ZipCPU/sdr/rtl/fmdemod.v

////////////////////////////////////////////////////////////////////////////////
//
// Filename: 	fmdemod.v
// {{{
// Project:	SDR, a basic Soft(Gate)ware Defined Radio architecture
//
// Purpose:	FM Demodulate an incoming I+Q (1-bit each) signal into the
//		underlying audio data.  The signal processing path includes;
//
//	1. CIC filter, to recover the lost bits from the I+Q sampling.  This
//		also downsamples the signal to a slower rate.
//	2. All but the top bits out of the CIC filter are then discarded
//	3. The result is then fed into an I+Q PLL, to track the frequency
//		of the incoming waveform
//	4. The PLL doesn't output frequency, however, it outputs phase.  The
//		difference between two phases is proportional to frequency,
//		so this difference is placed into a final resampler.
//	5. A gain is applied to the final (audio quality, hopefully) signal, and
//	6. Sent to a PWM audio output device.
//
// Creator:	Dan Gisselquist, Ph.D.
//		Gisselquist Technology, LLC
//
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
// This program is distributed in the hope that it will be useful, but WITHOUT
// ANY WARRANTY; without even the implied warranty of MERCHANTIBILITY or
// FITNESS FOR A PARTICULAR PURPOSE.  See the GNU General Public License
// for more details.
//
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
////////////////////////////////////////////////////////////////////////////////
//
//
`default_nettype	none
// }}}
module	fmdemod #(
		// {{{
		// parameter [31:0]	CLOCK_FREQUENCY_HZ = 36_000_000,
		// parameter [31:0]	RAW_DATA_RATE_HZ = 960_000,
		// parameter [31:0]	AUDIO_SAMPLE_RATE_HZ = 48_000,
		parameter		NUM_AUDIO_COEFFS = 666,
		parameter		HIST_BITS = 10,
		localparam	CIC_BITS = 7,
		localparam	BB_BITS  = 16,
		localparam	PWM_BITS = 16,
		localparam	PLL_BITS = 28,
		localparam [PLL_BITS-1:0]	DEFAULT_PLL_STEP = 0,
		//
		// localparam [31:0]	RAW_AUDIO_DOWNSAMPLE_RATIO
		//	= CLOCK_FREQUENCY_HZ / AUDIO_SAMPLE_RATE_HZ, // == 750
		// localparam [31:0]	RAW_AUDIO_DOWNSAMPLE_RATIO = 750,
		localparam		CIC_DOWN = 25,	// About 200kHz B/W
		// localparam		CIC_DOWN = 5,
		localparam [31:0]	SECONDARY_DOWNSAMPLE_RATIO
						= 750 / CIC_DOWN
		// }}}
	) (
		// {{{
		input	wire		i_clk, i_reset,
		input	wire		i_audio_en, i_rf_en,
		//
		// Wishbone interface
		// {{{
		input	wire		i_wb_cyc, i_wb_stb, i_wb_we,
		input	wire [1:0]	i_wb_addr,
		input	wire [31:0]	i_wb_data,
		input	wire	[3:0]	i_wb_sel,
		output	reg		o_wb_stall,
		output	reg		o_wb_ack,
		output	reg	[31:0]	o_wb_data,
		// }}}
		// Receive interface
		input	wire	[1:0]	i_rf_data,
		//
		// Outgoing PWM interface
		output	reg		o_pwm_audio,
		//
		// Debug interface
		// {{{
		input	wire	[1:0]	i_dbg_sel,
		output	reg		o_dbg_ce,
		output	reg	[31:0]	o_dbg_data,
		output reg [HIST_BITS-1:0] o_dbg_hist
		// }}}
		// }}}
	);

	// Signal declarations
	// {{{
	integer	k;

	wire			cic_ce, cic_ign, baseband_ce;
	wire	[CIC_BITS-1:0]	cic_sample_i, cic_sample_q;
	wire signed [BB_BITS-1:0] baseband_sample;
	reg	[PWM_BITS-1:0]	pwm_counter, brev_counter;
	reg signed [31:0]	amplified_sample;
	reg	[15:0]		audio_sample_off;
	// wire			splr_busy, splr_done;
	wire	[PLL_BITS-1:0]	pll_phase;
	reg	[PLL_BITS-1:0]	last_pll_phase, fm_step;
	reg	[4:0]		pll_lgcoeff;
	reg signed [15:0]	r_gain;
	reg			load_pll;
	reg	[PLL_BITS-2:0]	new_pll_step;
	reg			write_audio_filter, reset_filter;
	reg	[15:0]		write_coeff;
	wire	[1:0]		pll_err;
	wire			pll_locked;
	// }}}
	////////////////////////////////////////////////////////////////////////
	//
	// Incoming Bus processing
	// {{{
	////////////////////////////////////////////////////////////////////////
	//
	//
	initial	pll_lgcoeff  = 5'h05;
	initial	new_pll_step = DEFAULT_PLL_STEP[PLL_BITS-2:0];
	initial	load_pll     = 1;
	initial	reset_filter = 1;
	initial	write_audio_filter = 0;
	always @(posedge i_clk)
	if (i_wb_stb && i_wb_we)
	begin
		{ reset_filter, load_pll, write_coeff } <= 0;

		case(i_wb_addr)
		2'b00: r_gain <= i_wb_data[15:0];
		2'b01: { load_pll, new_pll_step } <= { 1'b1,  i_wb_data[PLL_BITS-2:0] };
		2'b10: { reset_filter, write_audio_filter, write_coeff }
				<= { i_wb_data[31], !i_wb_data[31],
						i_wb_data[15:0] };
		2'b11: pll_lgcoeff <= i_wb_data[4:0];
		default: begin end
		endcase
	end else
		{ reset_filter, load_pll, write_coeff } <= 0;

	always @(*)
		o_wb_stall = 1'b0;

	always @(posedge i_clk)
		o_wb_ack <= !i_reset && i_wb_stb;
	//  }}}
	////////////////////////////////////////////////////////////////////////
	//
	// CIC Filters
	// {{{
	////////////////////////////////////////////////////////////////////////
	//
	//
`ifdef	ALT_INCOMING_CIC
	reg	[7+2-1:0]	cic_acci	[0:7];
	reg	[7+2-1:0]	cic_accq	[0:7];
	reg	[7+2-1:0]	last_cic_acci	[0:6];
	reg	[7+2-1:0]	last_cic_accq	[0:6];
	reg	[1:0]		last_rf_data;

	always @(posedge i_clk)
	begin
		cic_acci[0] <= (i_rf_data[1] ? 9'h1ff : 9'h01)
				+ (last_rf_data[1] ? 9'h1ff : 9'h01);
		cic_accq[0] <= (i_rf_data[0] ? 9'h1ff : 9'h01)
				+ (last_rf_data[0] ? 9'h1ff : 9'h01);
		last_rf_data <= i_rf_data;
		{ last_cic_acci[0], last_cic_accq[0] }
				<= { cic_acci[0], cic_accq[0] };

		cic_acci[1] <= cic_acci[0] + last_cic_acci[0];
		cic_accq[1] <= cic_accq[0] + last_cic_accq[0];
		{ last_cic_acci[1], last_cic_accq[1] }
				<= { cic_acci[1], cic_accq[1] };

		cic_acci[2] <= cic_acci[1] + last_cic_acci[1];
		cic_accq[2] <= cic_accq[1] + last_cic_accq[1];
		{ last_cic_acci[2], last_cic_accq[2] }
				<= { cic_acci[2], cic_accq[2] };

		cic_acci[3] <= cic_acci[2] + last_cic_acci[2];
		cic_accq[3] <= cic_accq[2] + last_cic_accq[2];
		{ last_cic_acci[3], last_cic_accq[3] }
			<= { cic_acci[3], cic_accq[3] };

		cic_acci[4] <= cic_acci[3] + last_cic_acci[3];
		cic_accq[4] <= cic_accq[3] + last_cic_accq[3];
		{ last_cic_acci[4], last_cic_accq[4] }
			<= { cic_acci[4], cic_accq[4] };

		cic_acci[5] <= cic_acci[4] + last_cic_acci[4];
		cic_accq[5] <= cic_accq[4] + last_cic_accq[4];
		{ last_cic_acci[5], last_cic_accq[5] }
			<= { cic_acci[5], cic_accq[5] };

		cic_acci[6] <= cic_acci[5] + last_cic_acci[5];
		cic_accq[6] <= cic_accq[5] + last_cic_accq[5];
		{ last_cic_acci[6], last_cic_accq[6] }
			<= { cic_acci[6], cic_accq[6] };

		cic_acci[7] <= cic_acci[3] + last_cic_acci[6];
		cic_accq[7] <= cic_accq[3] + last_cic_accq[6];
		// { last_cic_acci[7], last_cic_accq[7] }
		//	<= { cic_acci[7], cic_accq[7] };
	end

	assign	cic_ce = 1'b1;

	assign	cic_sample_i = cic_acci[7][8:3] - 7'h10;
	assign	cic_sample_q = cic_accq[7][8:3]- 7'h10;
	assign	cic_ign = 1'b0;
`else

	cicfil #(.IW(2), .OW(CIC_BITS), .STAGES(4), .LGMEM(28), .SHIFT(10))
	cici(i_clk, reset_filter, CIC_DOWN[6:0], 1'b1, i_rf_data[1] ? 2'b01 : 2'b11, cic_ce, cic_sample_i);

	cicfil #(.IW(2), .OW(CIC_BITS), .STAGES(4), .LGMEM(28), .SHIFT(10))
	cicq(i_clk, reset_filter, CIC_DOWN[6:0], 1'b1, i_rf_data[0] ? 2'b01 : 2'b11, cic_ign, cic_sample_q);

`endif	// ALT_INCOMING_CIC
	// }}}
	////////////////////////////////////////////////////////////////////////
	//
	// Track the FM carrier
	// {{{
	////////////////////////////////////////////////////////////////////////
	//
	//

	quadpll #(.PHASE_BITS(PLL_BITS), .OPT_TRACK_FREQUENCY(1'b1),
		.INITIAL_PHASE_STEP(DEFAULT_PLL_STEP))// i.e. TRACKING FREQUENCY
	carrier_track(i_clk, load_pll, new_pll_step,
		cic_ce, { cic_sample_i[CIC_BITS-1], cic_sample_q[CIC_BITS-1] },
			pll_lgcoeff, pll_phase, pll_err, pll_locked);

	always @(posedge i_clk)
	if (cic_ce)
	begin
		fm_step <= pll_phase - last_pll_phase;
		last_pll_phase <= pll_phase;
	end

`ifdef	CIC_STEP
	reg	[PLL_BITS+7-1:0]	cic_step	[0:7];
	reg	[PLL_BITS+7-1:0]	last_step	[0:6];
	reg	[PLL_BITS+7-1:0]	last_fm_step;
	reg				step_ce;
	reg	[4:0]			step_counter;

	always @(posedge i_clk)
	if (cic_ce)
	begin
		cic_step[0] <= { {(7){fm_step[23]}}, fm_step } + last_fm_step;
		cic_step[1] <= cic_step[0] + last_step[0];
		cic_step[2] <= cic_step[1] + last_step[1];
		cic_step[3] <= cic_step[2] + last_step[2];
		cic_step[4] <= cic_step[3] + last_step[3];
		cic_step[5] <= cic_step[4] + last_step[4];
		cic_step[6] <= cic_step[5] + last_step[5];
		cic_step[7] <= cic_step[6] + last_step[6];

		last_fm_step <= { {(7){fm_step[23]}}, fm_step };
		last_step[0] <= cic_step[0];
		last_step[1] <= cic_step[1];
		last_step[2] <= cic_step[2];
		last_step[3] <= cic_step[3];
		last_step[4] <= cic_step[4];
		last_step[5] <= cic_step[5];
		last_step[6] <= cic_step[6];

		step_ce <= 0;
		step_counter <= step_counter - 1;
		if (step_counter == 0)
		begin
			step_ce <= 1;
			step_counter <= CIC_DOWN[4:0]-1;
		end
	end else
		step_ce <= 0;
`endif
	// }}}
	////////////////////////////////////////////////////////////////////////
	//
	// Downsampling (PLL cleanup)
	// {{{
	////////////////////////////////////////////////////////////////////////
	//
	//

	subfildown #(.IW(BB_BITS), .OW(BB_BITS), .CW(12),
		.INITIAL_COEFFS("amdemod.hex"),
		.SHIFT(10),
		.NDOWN(SECONDARY_DOWNSAMPLE_RATIO),
		.FIXED_COEFFS(1'b0), .NCOEFFS(NUM_AUDIO_COEFFS))
	resample(i_clk, reset_filter,
		write_audio_filter, write_coeff[15:4],
		// cic_ce, cic_step[7][PLL_BITS+7-3-1:PLL_BITS+7-3-BB_BITS],
		cic_ce, fm_step[PLL_BITS-1:PLL_BITS-BB_BITS],
		baseband_ce, baseband_sample);
	// }}}
	////////////////////////////////////////////////////////////////////////
	//
	// Amplify the result
	// {{{
	////////////////////////////////////////////////////////////////////////
	//
	//

	(* mul2dsp *)
	always @(posedge  i_clk)
	// if (splr_done)
		amplified_sample <= baseband_sample[15:0] * r_gain;
	// }}}
	////////////////////////////////////////////////////////////////////////
	//
	// Convert to PWM
	// {{{
	////////////////////////////////////////////////////////////////////////
	//
	//

	always @(posedge  i_clk)
	// if (splr_done)
	begin
		audio_sample_off[14:0] <=  amplified_sample[30:16];
		audio_sample_off[15]   <= !amplified_sample[31];
	end

	always @(posedge i_clk)
		pwm_counter <= pwm_counter + 1;

	always @(*)
	for(k=0; k<PWM_BITS; k=k+1)
		brev_counter[k] = pwm_counter[PWM_BITS-1-k];

	always @(posedge i_clk)
	if (!i_audio_en)
		o_pwm_audio <= !o_pwm_audio;
	else
		o_pwm_audio <= (brev_counter < audio_sample_off);

	// }}}
	////////////////////////////////////////////////////////////////////////
	//
	// Create the debugging outputs
	// {{{
	////////////////////////////////////////////////////////////////////////
	//
	//

	always @(posedge i_clk)
	case(i_dbg_sel)
	2'b00: { o_dbg_ce, o_dbg_data, o_dbg_hist } <= { cic_ce,
			{(16-CIC_BITS){cic_sample_i[CIC_BITS-1]}}, cic_sample_i,
			{(16-CIC_BITS){cic_sample_q[CIC_BITS-1]}}, cic_sample_q,
			cic_sample_i[CIC_BITS-1:CIC_BITS-(HIST_BITS/2)],
			cic_sample_q[CIC_BITS-1:CIC_BITS-(HIST_BITS/2)] };
	2'b10: { o_dbg_ce, o_dbg_data, o_dbg_hist } <= { cic_ce,
				{(32-PLL_BITS){1'b0}}, fm_step,
				fm_step[PLL_BITS-1:PLL_BITS-HIST_BITS] };
	2'b01: { o_dbg_ce, o_dbg_data, o_dbg_hist } <= { baseband_ce,
				{(32-BB_BITS){1'b0}}, baseband_sample,
				baseband_sample[BB_BITS-1:BB_BITS-HIST_BITS] };
	2'b11: { o_dbg_ce, o_dbg_data, o_dbg_hist }
			<= { baseband_ce, amplified_sample,
			amplified_sample[32-1:32-HIST_BITS] };
	default: { o_dbg_ce, o_dbg_data, o_dbg_hist } <= 0;
	endcase

	always @(*)
		o_wb_data = o_dbg_data;
	// }}}

	// Make Verilator happy
	// {{{
	// Verilator lint_off UNUSED
	wire	unused;
	assign	unused = &{ 1'b0, i_wb_cyc, i_wb_sel,
			cic_ign,
			i_rf_en, write_coeff[3:0], pll_err, i_wb_data[30:23],
			amplified_sample[15:0], fm_step[23:16],
			write_audio_filter, write_coeff, pll_locked };
	// Verilator lint_on  UNUSED
	// }}}
endmodule
