ZipCPU/sdr/rtl/seqcordic.v

////////////////////////////////////////////////////////////////////////////////
//
// Filename: 	seqcordic.v
// {{{
// Project:	SDR, a basic Soft(Gate)ware Defined Radio architecture
//
// Purpose:	This file executes a vector rotation on the values
//		(i_xval, i_yval).  This vector is rotated left by
//	i_phase.  i_phase is given by the angle, in radians, multiplied by
//	2^32/(2pi).  In that fashion, a two pi value is zero just as a zero
//	angle is zero.
//
//	This particular version of the CORDIC processes one value at a
//	time in a sequential, vs pipelined or parallel, fashion.
//
// Creator:	Dan Gisselquist, Ph.D.
//		Gisselquist Technology, LLC
//
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
// This program is distributed in the hope that it will be useful, but WITHOUT
// ANY WARRANTY; without even the implied warranty of MERCHANTIBILITY or
// FITNESS FOR A PARTICULAR PURPOSE.  See the GNU General Public License
// for more details.
//
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
//
////////////////////////////////////////////////////////////////////////////////
//
//
`default_nettype	none
// }}}
module	seqcordic #(
		// {{{
		// These parameters are fixed by the core generator.  They
		// have been used in the definitions of internal constants,
		// so they can't really be changed here.
		localparam	IW= 8,	// The number of bits in our inputs
				OW= 8,	// The number of output bits to produce
				// NSTAGES=11,
				// XTRA= 3,// Extra bits for internal precision
				WW=11,	// Our working bit-width
				PW=16	// Bits in our phase variables
		// }}}
	) (
		// {{{
		input	wire				i_clk, i_reset, i_stb,
		input	wire	signed	[(IW-1):0]	i_xval, i_yval,
		input	wire		[(PW-1):0]	i_phase,
		output	wire				o_busy,
		output	reg				o_done,
		output	reg	signed	[(OW-1):0]	o_xval, o_yval
		// }}}
	);
	// First step: expand our input to our working width.
	// {{{
	// This is going to involve extending our input by one
	// (or more) bits in addition to adding any xtra bits on
	// bits on the right.  The one bit extra on the left is to
	// allow for any accumulation due to the cordic gain
	// within the algorithm.
	// 
	wire	signed [(WW-1):0]	e_xval, e_yval;
	assign	e_xval = { {i_xval[(IW-1)]}, i_xval, {(WW-IW-1){1'b0}} };
	assign	e_yval = { {i_yval[(IW-1)]}, i_yval, {(WW-IW-1){1'b0}} };

	// }}}
	// Declare variables for all of the separate stages
	// {{{
	reg	signed	[(WW-1):0]	xv, prex, yv, prey;
	reg		[(PW-1):0]	ph, preph;
	reg				idle, pre_valid;
	reg		[3:0]		state;

	// First step, get rid of all but the last 45 degrees
	// {{{
	// The resulting phase needs to be between -45 and 45
	// degrees but in units of normalized phase
	//
	// We'll do this by walking through all possible quick phase
	// shifts necessary to constrain the input to within +/- 45
	// degrees.
	always @(posedge i_clk)
	case(i_phase[(PW-1):(PW-3)])
	3'b000: begin	// 0 .. 45, No change
		// {{{
		prex  <=  e_xval;
		prey  <=  e_yval;
		preph <= i_phase;
		end
		// }}}
	3'b001: begin	// 45 .. 90
		// {{{
		prex  <= -e_yval;
		prey  <=  e_xval;
		preph <= i_phase - 16'h4000;
		end
		// }}}
	3'b010: begin	// 90 .. 135
		// {{{
		prex  <= -e_yval;
		prey  <=  e_xval;
		preph <= i_phase - 16'h4000;
		end
		// }}}
	3'b011: begin	// 135 .. 180
		// {{{
		prex  <= -e_xval;
		prey  <= -e_yval;
		preph <= i_phase - 16'h8000;
		end
		// }}}
	3'b100: begin	// 180 .. 225
		// {{{
		prex  <= -e_xval;
		prey  <= -e_yval;
		preph <= i_phase - 16'h8000;
		end
		// }}}
	3'b101: begin	// 225 .. 270
		// {{{
		prex  <=  e_yval;
		prey  <= -e_xval;
		preph <= i_phase - 16'hc000;
		end
		// }}}
	3'b110: begin	// 270 .. 315
		// {{{
		prex  <=  e_yval;
		prey  <= -e_xval;
		preph <= i_phase - 16'hc000;
		end
		// }}}
	3'b111: begin	// 315 .. 360, No change
		// {{{
		prex  <=  e_xval;
		prey  <=  e_yval;
		preph <= i_phase;
		end
		// }}}
	endcase
	// }}}

	// Cordic angle table
	// {{{
	// In many ways, the key to this whole algorithm lies in the angles
	// necessary to do this.  These angles are also our basic reason for
	// building this CORDIC in C++: Verilog just can't parameterize this
	// much.  Further, these angle's risk becoming unsupportable magic
	// numbers, hence we define these and set them in C++, based upon
	// the needs of our problem, specifically the number of stages and
	// the number of bits required in our phase accumulator
	//
	reg	[15:0]	cordic_angle [0:15];
	reg	[15:0]	cangle;

	initial	cordic_angle[ 0] = 16'h12e4; //  26.565051 deg
	initial	cordic_angle[ 1] = 16'h09fb; //  14.036243 deg
	initial	cordic_angle[ 2] = 16'h0511; //   7.125016 deg
	initial	cordic_angle[ 3] = 16'h028b; //   3.576334 deg
	initial	cordic_angle[ 4] = 16'h0145; //   1.789911 deg
	initial	cordic_angle[ 5] = 16'h00a2; //   0.895174 deg
	initial	cordic_angle[ 6] = 16'h0051; //   0.447614 deg
	initial	cordic_angle[ 7] = 16'h0028; //   0.223811 deg
	initial	cordic_angle[ 8] = 16'h0014; //   0.111906 deg
	initial	cordic_angle[ 9] = 16'h000a; //   0.055953 deg
	initial	cordic_angle[10] = 16'h0005; //   0.027976 deg
	initial	cordic_angle[11] = 16'h0002; //   0.013988 deg
	initial	cordic_angle[12] = 16'h0001; //   0.006994 deg
	initial	cordic_angle[13] = 16'h0000; //   0.003497 deg
	initial	cordic_angle[14] = 16'h0000; //   0.001749 deg
	initial	cordic_angle[15] = 16'h0000; //   0.000874 deg
	// {{{
	// Std-Dev    : 0.00 (Units)
	// Phase Quantization: 0.000183 (Radians)
	// Gain is 1.164435
	// You can annihilate this gain by multiplying by 32'hdbd95b16
	// and right shifting by 32 bits.
	// }}}
	// }}}

	// idle
	// {{{
	initial	idle = 1'b1;
	always @(posedge i_clk)
	if (i_reset)
		idle <= 1'b1;
	else if (i_stb)
		idle <= 1'b0;
	else if (state == 10)
		idle <= 1'b1;
	// }}}

	// pre_valid
	// {{{
	initial	pre_valid = 1'b0;
	always @(posedge i_clk)
	if (i_reset)
		pre_valid <= 1'b0;
	else
		pre_valid <= (i_stb)&&(idle);
	// }}}

	// cangle - CORDIC angle table lookup
	// {{{
	always @(posedge i_clk)
		cangle <= cordic_angle[state];
	// }}}

	// state
	// {{{
	initial	state = 0;
	always @(posedge i_clk)
	if (i_reset)
		state <= 0;
	else if (idle)
		state <= 0;
	else if (state == 10)
		state <= 0;
	else
		state <= state + 1;
	// }}}

	// CORDIC rotations
	// {{{
	// Here's where we are going to put the actual CORDIC
	// we've been studying and discussing.  Everything up to
	// this point has simply been necessary preliminaries.
	always @(posedge i_clk)
	if (pre_valid)
	begin
		// {{{
		xv <= prex;
		yv <= prey;
		ph <= preph;
		// }}}
	end else if (ph[PW-1])
	begin
		// {{{
		xv <= xv + (yv >>> state);
		yv <= yv - (xv >>> state);
		ph <= ph + (cangle);
		// }}}
	end else begin
		// {{{
		xv <= xv - (yv >>> state);
		yv <= yv + (xv >>> state);
		ph <= ph - (cangle);
		// }}}
	end
	// }}}

	// Round our result towards even
	// {{{
	wire	[(WW-1):0]	final_xv, final_yv;

	assign	final_xv = xv + $signed({{(OW){1'b0}},
				xv[(WW-OW)],
				{(WW-OW-1){!xv[WW-OW]}} });
	assign	final_yv = yv + $signed({{(OW){1'b0}},
				yv[(WW-OW)],
				{(WW-OW-1){!yv[WW-OW]}} });
	// }}}
	// o_done
	// {{{
	initial	o_done = 1'b0;
	always @(posedge i_clk)
	if (i_reset)
		o_done <= 1'b0;
	else
		o_done <= (state >= 10);
	// }}}

	// Output assignments: o_xval, o_yval
	// {{{
	always @(posedge i_clk)
	if (state >= 10)
	begin
		o_xval <= final_xv[WW-1:WW-OW];
		o_yval <= final_yv[WW-1:WW-OW];
	end
	// }}}

	assign	o_busy = !idle;

	// Make Verilator happy with pre_.val
	// {{{
	// verilator lint_off UNUSED
	wire	unused_val;
	assign	unused_val = &{ 1'b0,  final_xv[WW-OW-1:0], final_yv[WW-OW-1:0] };
	// verilator lint_on UNUSED
	// }}}
endmodule
