ZipCPU/sdr/rtl/wbgpio.v

////////////////////////////////////////////////////////////////////////////////
//
// Filename:	wbgpio.v
// {{{
// Project:	SDR, a basic Soft(Gate)ware Defined Radio architecture
//
// Purpose:	This extremely simple GPIO controller, although minimally 
//		featured, is designed to control up to sixteen general purpose
//	input and sixteen general purpose output lines of a module from a
//	single address on a 32-bit wishbone bus.
//
//	Input GPIO values are contained in the top 16-bits.  Any change in
//	input values will generate an interrupt.
//
//	Output GPIO values are contained in the bottom 16-bits.  To change an
//	output GPIO value, writes to this port must also set a bit in the
//	upper sixteen bits.  Hence, to set GPIO output zero, one would write
//	a 0x010001 to the port, whereas a 0x010000 would clear the bit.  This
//	interface makes it possible to change only the bit of interest, without
//	needing to capture and maintain the prior bit values--something that
//	might be difficult from a interrupt context within a CPU.
//	
//	Unlike other controllers, this controller offers no capability to
//	change input/output direction, or to implement pull-up or pull-down
//	resistors.  It simply changes and adjusts the values going out the
//	output pins, while allowing a user to read the values on the input
//	pins.
//
//	Any change of an input pin value will result in the generation of an
//	interrupt signal.
//
// Creator:	Dan Gisselquist, Ph.D.
//		Gisselquist Technology, LLC
//
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
// This program is distributed in the hope that it will be useful, but WITHOUT
// ANY WARRANTY; without even the implied warranty of MERCHANTIBILITY or
// FITNESS FOR A PARTICULAR PURPOSE.  See the GNU General Public License
// for more details.
//
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
//
////////////////////////////////////////////////////////////////////////////////
//
//
`default_nettype	none
// }}}
module wbgpio #(
		// {{{
		parameter		NIN=16, NOUT=16,
		parameter [(NOUT-1):0]	DEFAULT=0
		// }}}
	) (
		// {{{
		input	wire			i_clk,
		// Wishbone interface
		// {{{
		input	wire			i_wb_cyc, i_wb_stb, i_wb_we,
		input	wire	[31:0]		i_wb_data,
		input	wire	[3:0]		i_wb_sel,
		output	wire			o_wb_stall, o_wb_ack,
		output	wire	[31:0]		o_wb_data,
		// }}}
		// GPIO pins
		// {{{
		input	wire	[(NIN-1):0]	i_gpio,
		output	reg	[(NOUT-1):0]	o_gpio,
		// }}}
		// Pin changed interrupt
		output	reg			o_int
		// }}}
	);

	// Signal declarations
	// {{{
	reg	[(NIN-1):0]	x_gpio, q_gpio, r_gpio;
	reg	[15:0]		hi_bits, low_bits;
	// }}}

	// o_gpio
	// {{{
	// 9LUT's, 16 FF's
	initial	o_gpio = DEFAULT;
	always @(posedge i_clk)
	if ((i_wb_stb)&&(i_wb_we))
		o_gpio <= ((o_gpio)&(~i_wb_data[(NOUT+16-1):16]))
			|((i_wb_data[(NOUT-1):0])&(i_wb_data[(NOUT+16-1):16]));
	// }}}

	// Incoming GPIO clock crossing, and interrupt generation
	// {{{
	// 3 LUTs, 33 FF's
	always @(posedge i_clk)
	begin
		x_gpio <= i_gpio;
		q_gpio <= x_gpio;
		r_gpio <= q_gpio;
		o_int  <= (x_gpio != r_gpio);
	end
	// }}}

	always @(*)
	begin
		low_bits = 0;
		hi_bits  = 0;
		low_bits[NOUT-1:0] = o_gpio;
		hi_bits[NIN-1:0]   = r_gpio;
	end

	assign	o_wb_stall = 1'b0;
	assign	o_wb_ack   = i_wb_stb;
	assign	o_wb_data = { hi_bits, low_bits };

	// Make Verilator happy
	// {{{
	// verilator lint_off UNUSED
	wire	unused;
	assign	unused = &{ 1'b0, i_wb_cyc, i_wb_data[31:0], i_wb_sel };
	// verilator lint_on  UNUSED
	// }}}
endmodule
